sdalimon/TeensyMeter/Sim/TeensyMeterAmp.asc

R1: res; 10k
R2: res; 10k
R3: res; 10Meg
R4: res; 10Meg
R5: res; 221k
R6: res; 221k
U1: UniversalOpamp2; Avol=316227 GBW=5Meg Slew=2.5Meg; ilimit=25m rail=15m Vos=0 phimargin=65
U2: UniversalOpamp2; Avol=316227 GBW=5Meg Slew=2.5Meg; ilimit=25m rail=15m Vos=0 phimargin=65
V1: voltage; 3.3
V2: voltage; SINE(0 60 60); AC 1
Named nets: 0, REF_HALF, AREF, OUT, INP, INN
.tran 200m
